reelbeelveel/binary_clock/EAGLE/control/images/control_brd_rev1_full.png

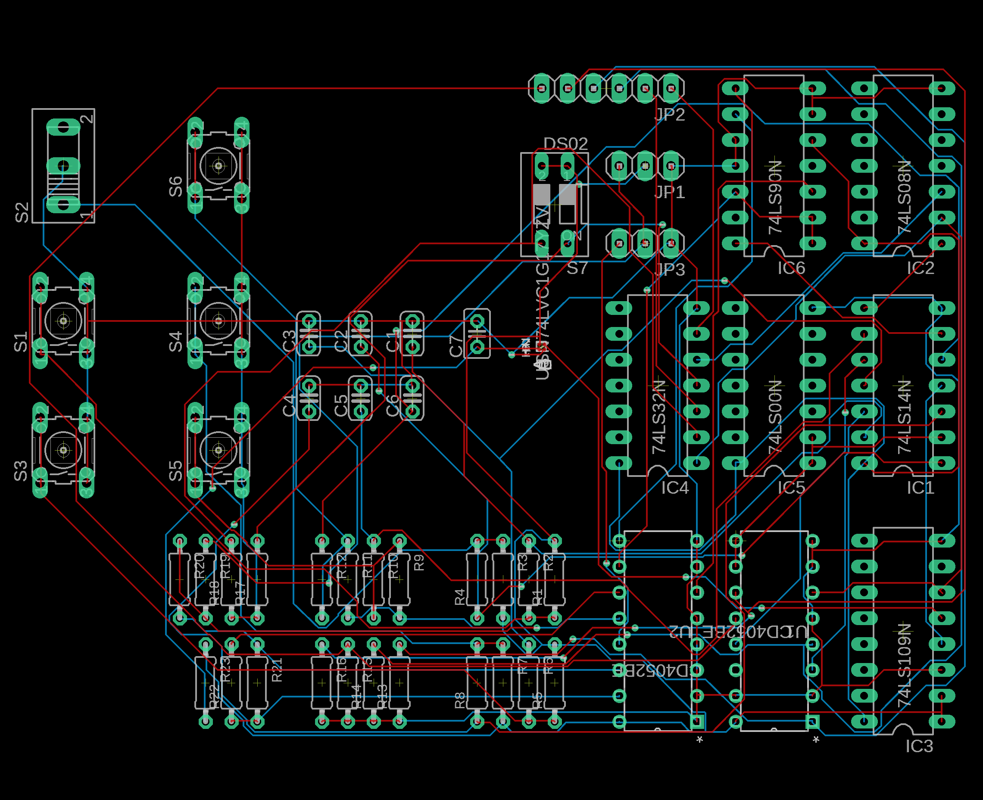
EAGLE/control/images/control_brd_rev1_full.png
