reelbeelveel/binary_clock/EAGLE/control/images/control_sch_rev1_full_light.png

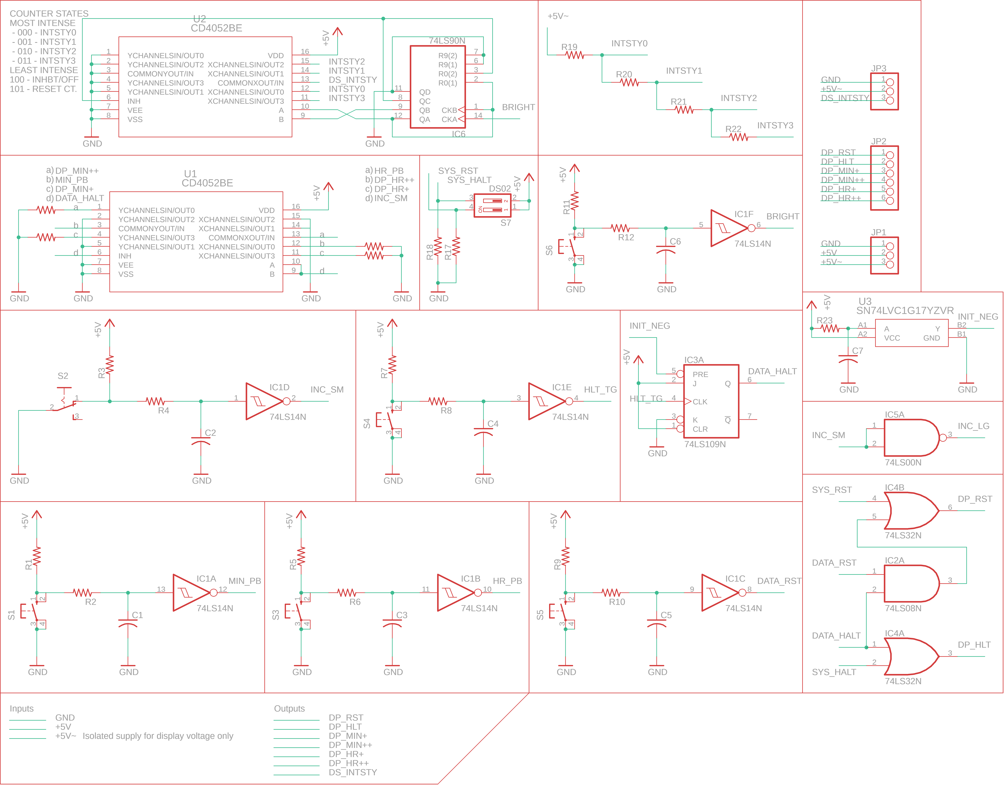
EAGLE/control/images/control_sch_rev1_full_light.png
