reelbeelveel/binary_clock/EAGLE/control/images/control_sch_rev1_misc.png

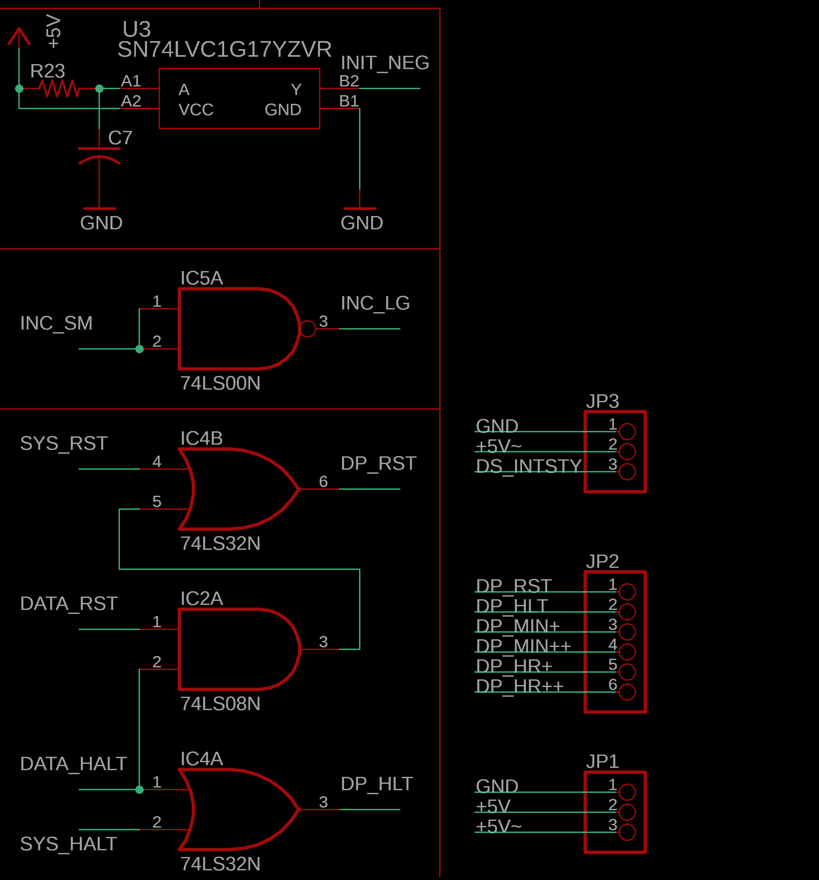
EAGLE/control/images/control_sch_rev1_misc.png
