reelbeelveel/binary_clock/EAGLE/datapath/images/clock_datapath_rev2_full_light.png

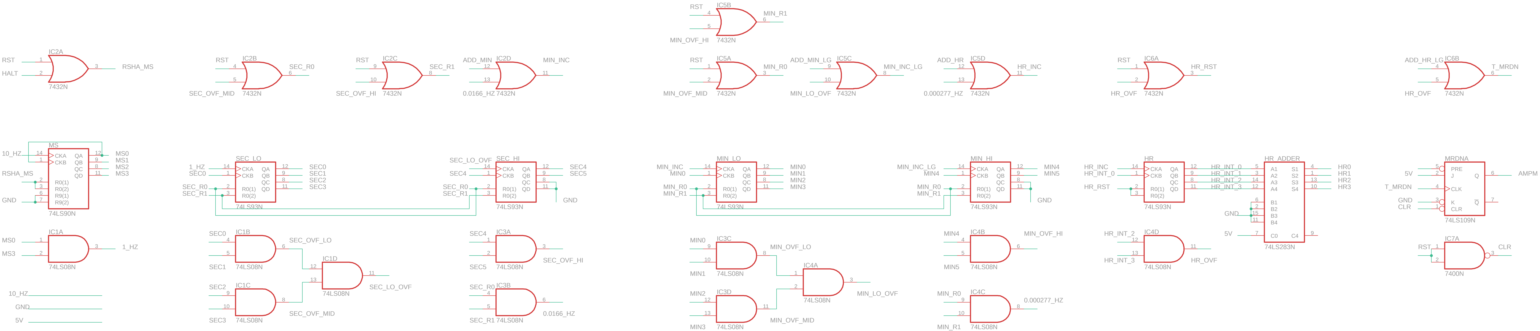
EAGLE/datapath/images/clock_datapath_rev2_full_light.png
