reelbeelveel/binary_clock/EAGLE/datapath/images/rev2_min_hr.png

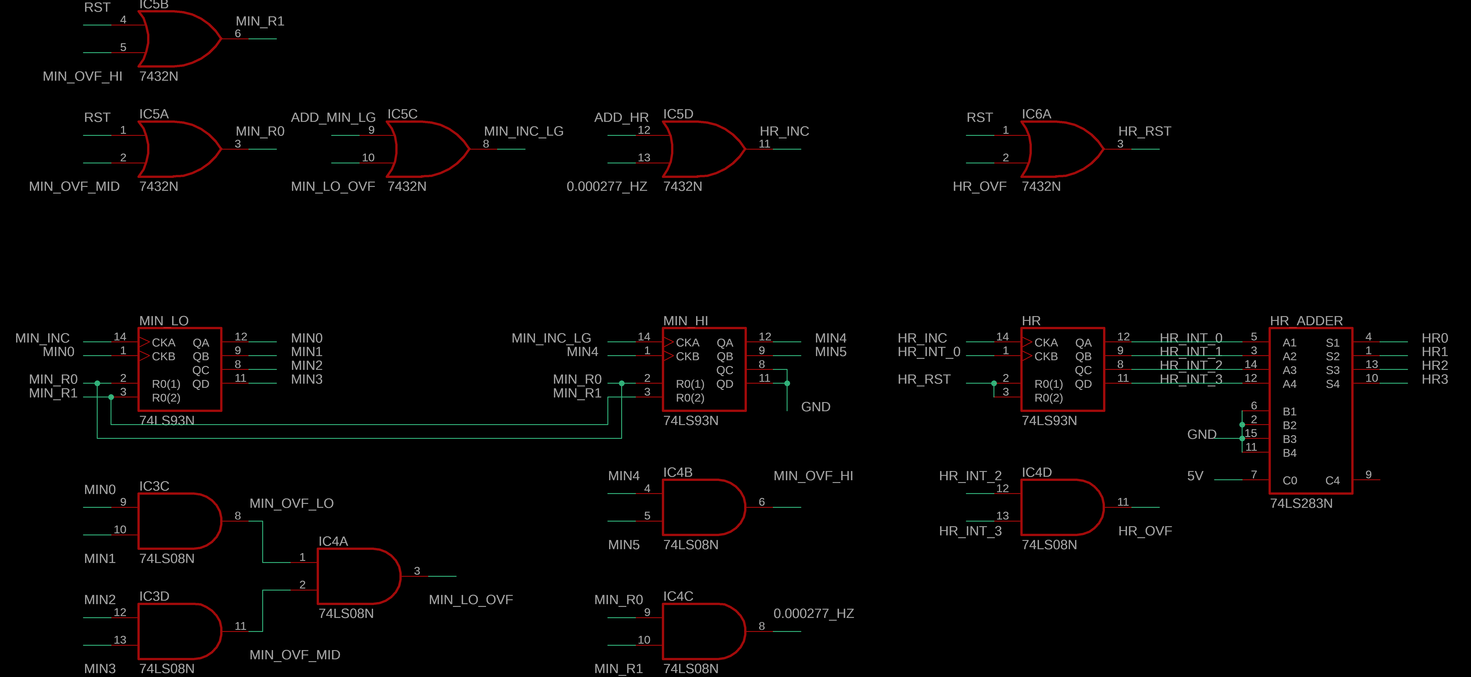
EAGLE/datapath/images/rev2_min_hr.png
